marcelomrocha/fred-robot/fred-prjt-photos/20230122_070132.jpg

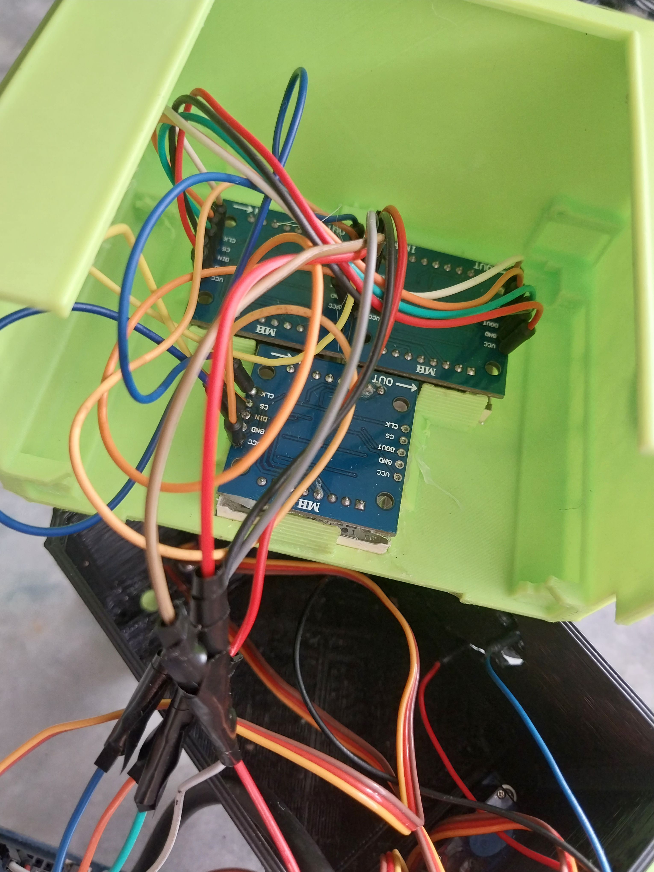
fred-prjt-photos/20230122_070132.jpg
