marcelomrocha/fred-robot/fred-prjt-photos/20230122_070137.jpg

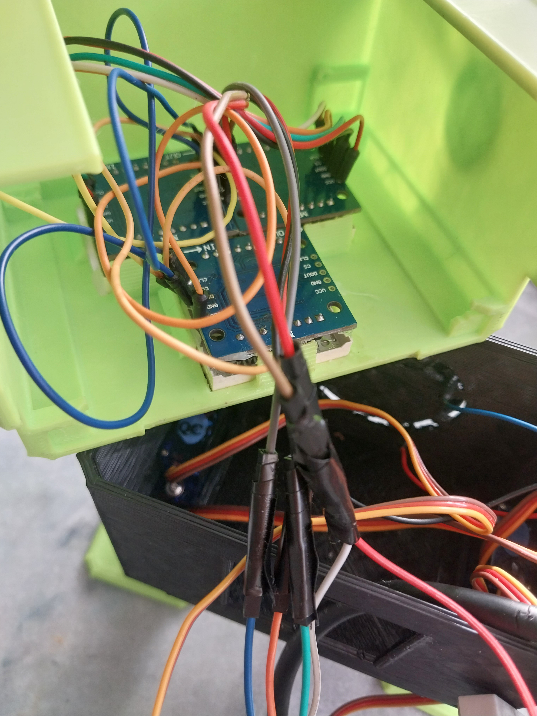
fred-prjt-photos/20230122_070137.jpg
