marcelomrocha/fred-robot/fred-3D-models/fred-girl-heart.stl

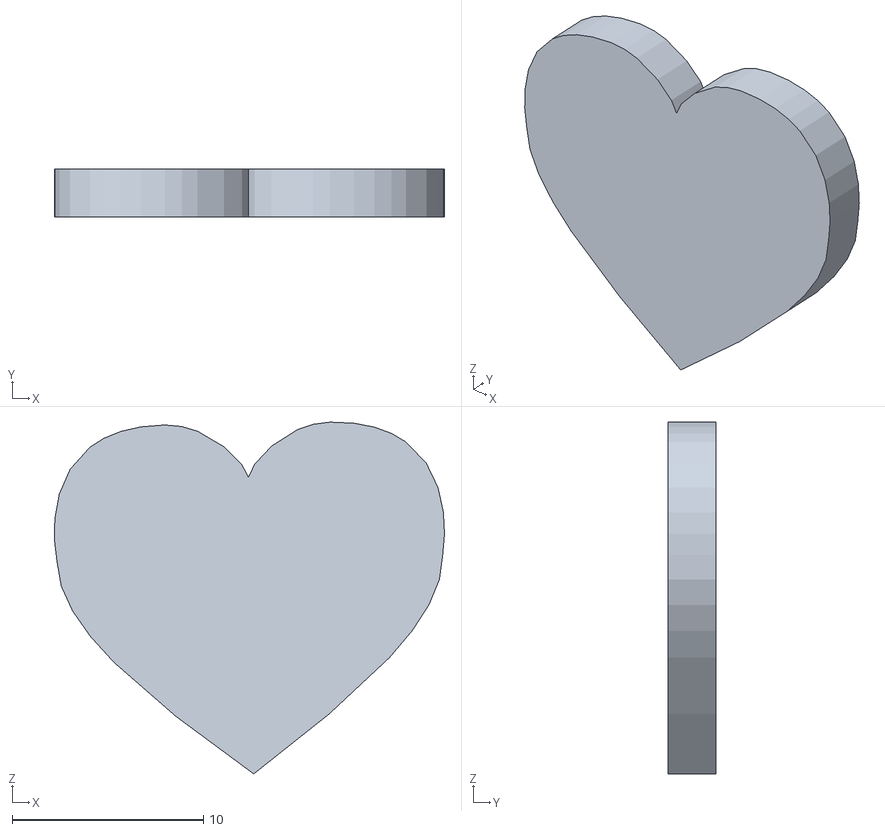
[picture p23: CAD file, 2025-06-29]
fred-3D-models/fred-girl-heart.stl
20.4 x 2.50 x 18.4
