marcelomrocha/fred-robot/fred-3D-models/fred-girl-head.stl

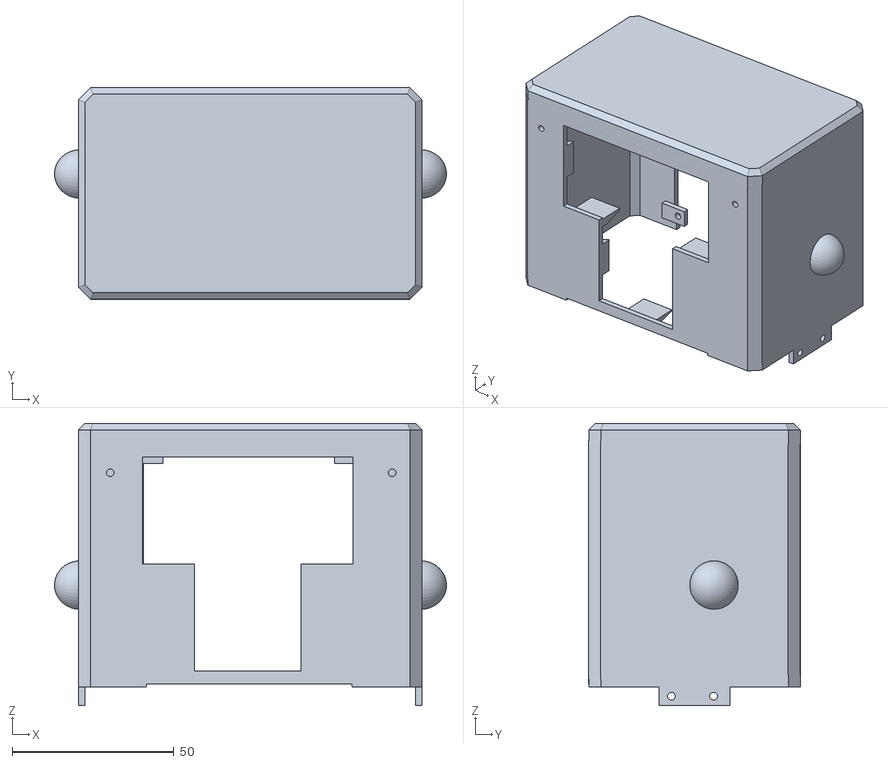
[picture p24: CAD file, 2025-06-29]
fred-3D-models/fred-girl-head.stl
121.0 x 65.4 x 87.1
