marcelomrocha/fred-robot/fred-3D-models/fred-shoulder.stl

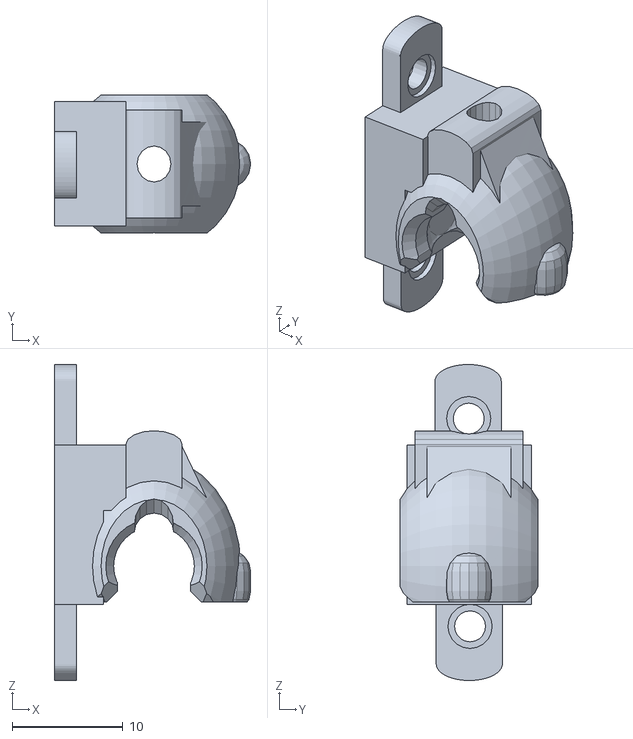
[picture p25: CAD file, 2025-06-29]
fred-3D-models/fred-shoulder.stl
17.8 x 12.5 x 28.6
