marcelomrocha/fred-robot/fred-3D-models/fred-arm.stl

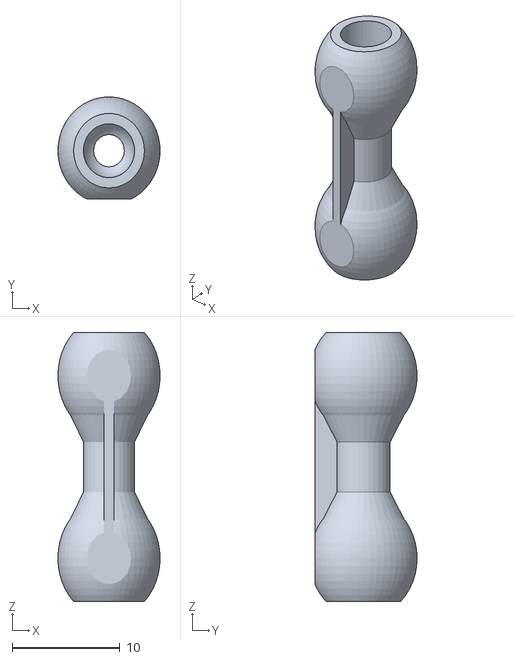
[picture p26: CAD file, 2025-06-29]
fred-3D-models/fred-arm.stl
9.50 x 9.50 x 25.0
