marcelomrocha/fred-robot/fred-3D-models/fred-boy-glasses.stl

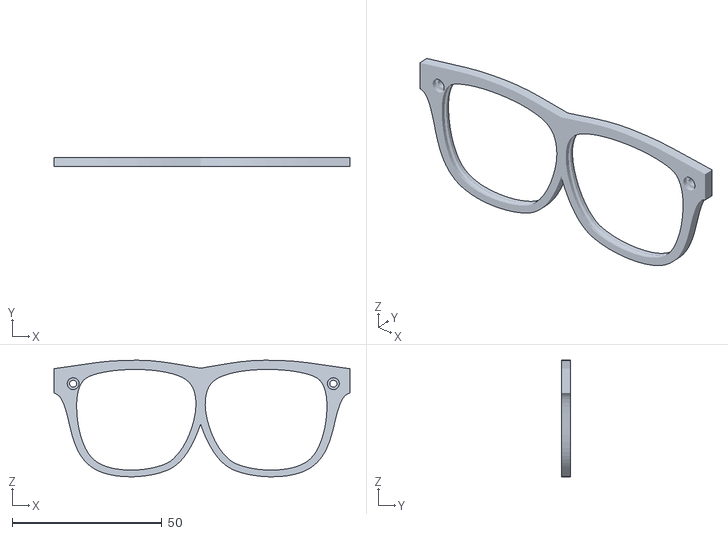
[picture p27: CAD file, 2025-06-29]
fred-3D-models/fred-boy-glasses.stl
99.0 x 3.00 x 39.0
