marcelomrocha/fred-robot/fred-control/FredControl/FredControl.h

typedef struct // expression struct definition
{
  char * right_eye;
  char * left_eye;
  char * mouth;
} Expression; // type Gaze

// valores para calibragem do equilibrio das pernas e pés
char LEG_LEFT_EQ = 95;
char FOOT_LEFT_EQ = 80;
char LEG_RIGHT_EQ = 86;
char FOOT_RIGHT_EQ = 95;
