marcelomrocha/fred-robot/fred-control/FredControl/FredSymbols.h

/* symbols definitions */


byte fr[8]={ // fr
B11100000,
B10000000,
B11100000,
B10000000,
B10111000,
B00100100,
B00111000,
B00100100};

byte ed[8]={ // ed
B01110000,
B01000000,
B01110000,
B01000000,
B01111110,
B00001001,
B00001001,
B00001110};


byte heart[8]={ // heart
B00000000,
B01100110,
B11111111,
B11111111,
B01111110,
B00111100,
B00011000,
B00000000};

// in love images maps
byte r_eye_in_love[8]={ // right eye
B01110000,
B10000000,
B00010100,
B00111110,
B00111110,
B00011100,
B00001000,
B00000000};

byte l_eye_in_love[8]={ // left eye
B00001110,
B00000001,
B00101000,
B01111100,
B01111100,
B00111000,
B00010000,
B00000000};

byte m_in_love[8]={ // mouth
B00000000,
B00000000,
B00000000,
B01000010,
B00111100,
B00000000,
B00000000,
B00000000};

// broken images maps
byte r_eye_broken[8]={ // right eye
B00000000,
B00000000,
B00001000,
B00001000,
B00111110,
B00001000,
B00001000,
B00000000};

byte l_eye_in_broken[8]={ // left eye
B00000000,
B00000000,
B00010000,
B00010000,
B01111100,
B00010000,
B00010000,
B00000000};

byte m_in_broken[8]={ // mouth
B00000000,
B00000000,
B00000000,
B00000000,
B00111100,
B01000010,
B00000000,
B00000000};


// neutral images maps
byte r_eye_neutral[8]={ // right eye
B00000000,
B00111100,
B01000010,
B00001000,
B00011100,
B00011100,
B00001000,
B00000000};

byte l_eye_neutral[8]={ // left eye
B00000000,
B00111100,
B01000010,
B00010000,
B00111000,
B00111000,
B00010000,
B00000000};

byte m_neutral[8]={ // mouth
B00000000,
B00000000,
B00000000,
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
B00000000,
B00000000};

// mouth_close
byte m_close[8]={ // mouth close
B00000000,
B00000000,
B00000000,
B00111100,
B00000000,
B00000000,
B00000000,
B00000000};

// mouth_mid
byte m_mid[8]={ // mouth close
B00000000,
B00000000,
B00011000,
B00111100,
B00011000,
B00000000,
B00000000,
B00000000};
